HDrizzle/stack_machine/kicad/rendering_output/motherboard_render.png

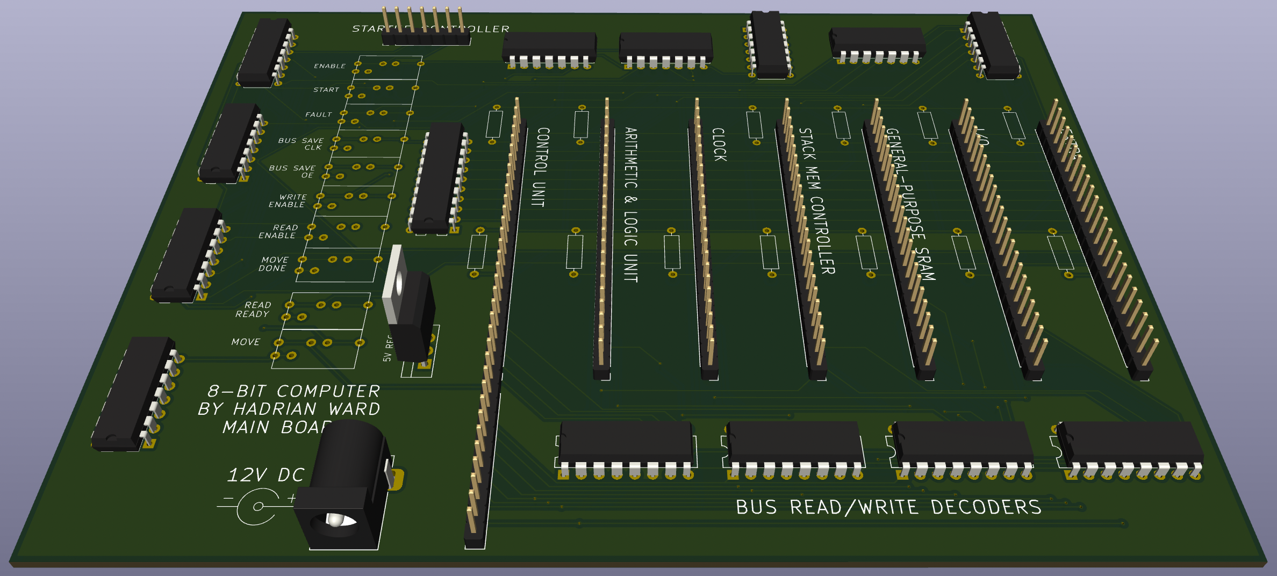
kicad/rendering_output/motherboard_render.png
