HDrizzle/stack_machine/presentation/images/actual_sequencer_cv.png

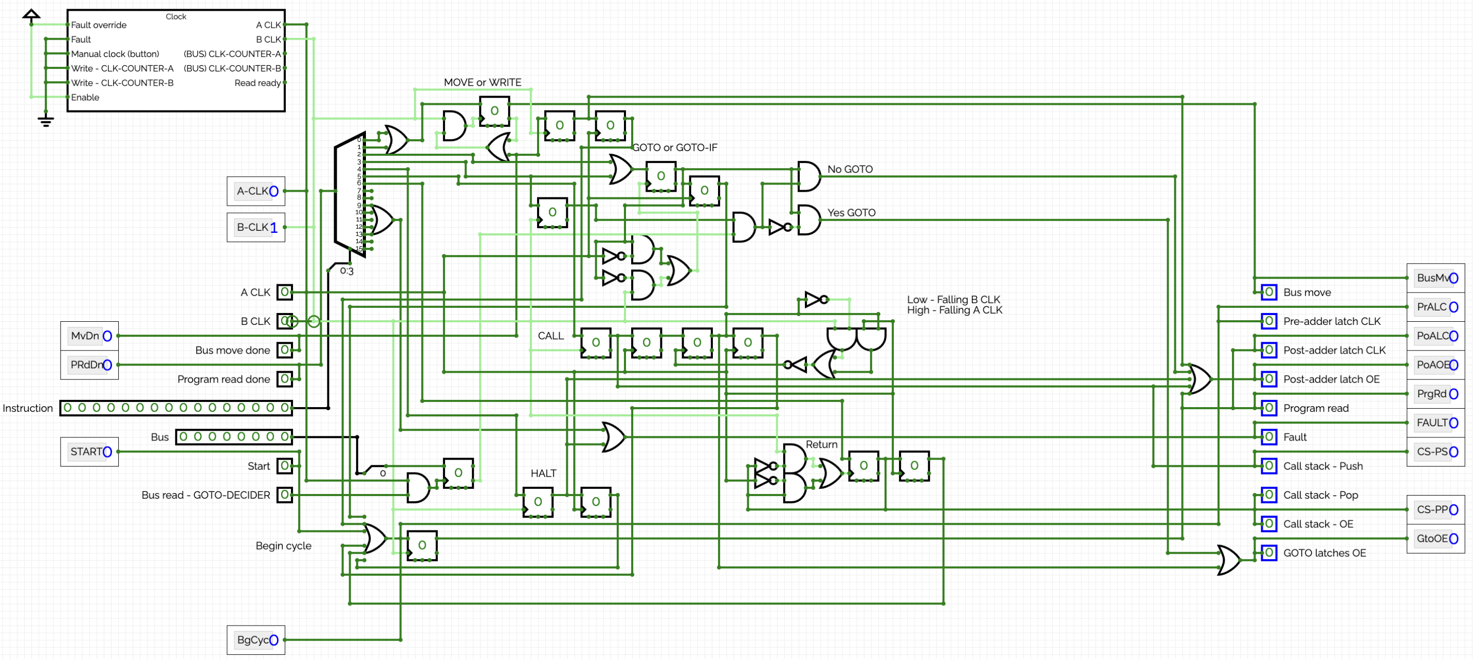
presentation/images/actual_sequencer_cv.png
