HDrizzle/stack_machine/presentation/images/bin_to_hex_gsheets.png

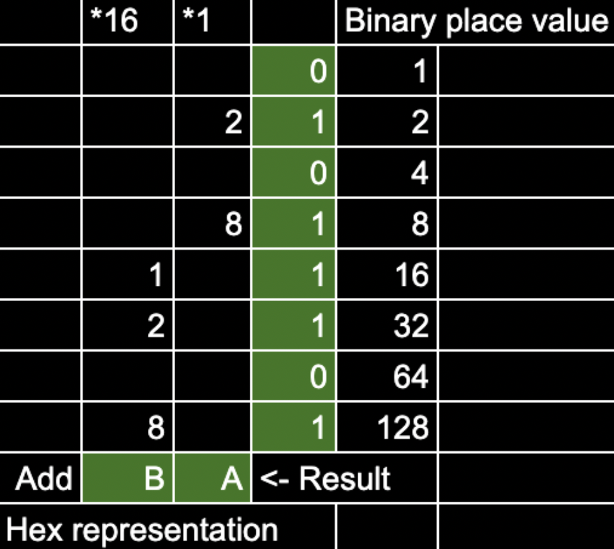
presentation/images/bin_to_hex_gsheets.png
