HDrizzle/stack_machine/presentation/images/bus_board.jpg

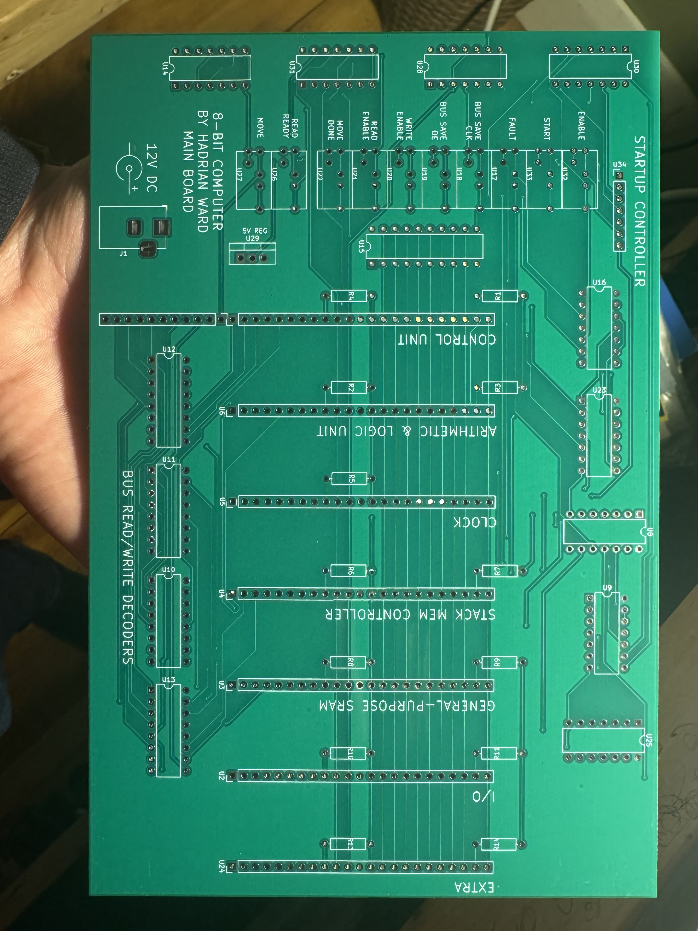
presentation/images/bus_board.jpg
