HDrizzle/stack_machine/presentation/images/bus_board_on_laptop.JPG

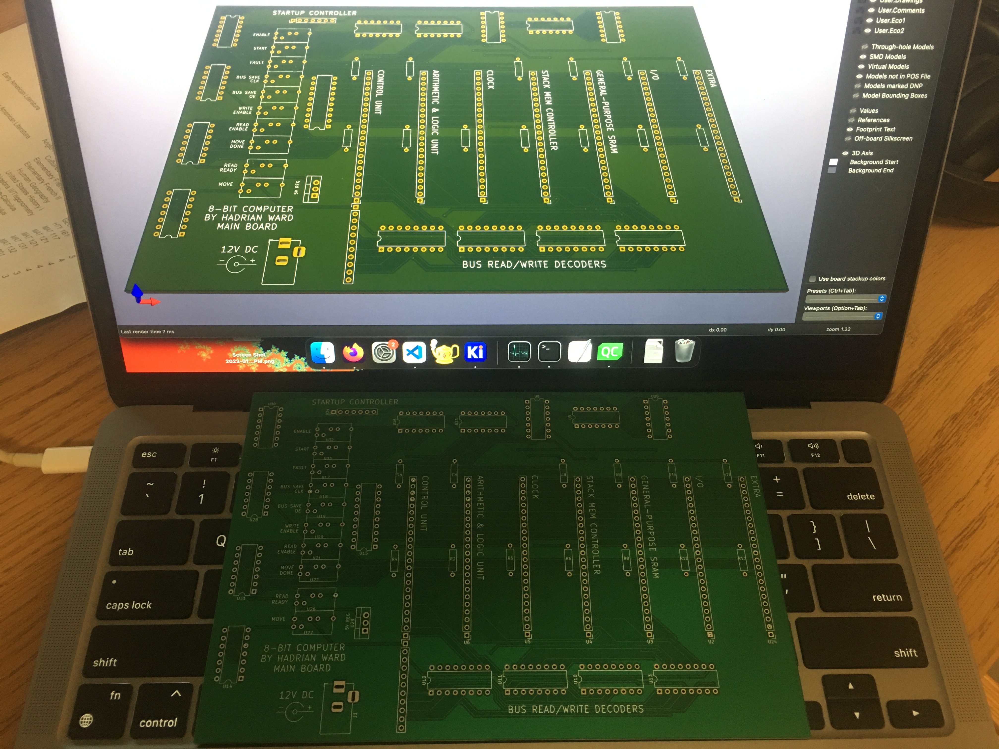
presentation/images/bus_board_on_laptop.JPG
