HDrizzle/stack_machine/presentation/images/chips.png

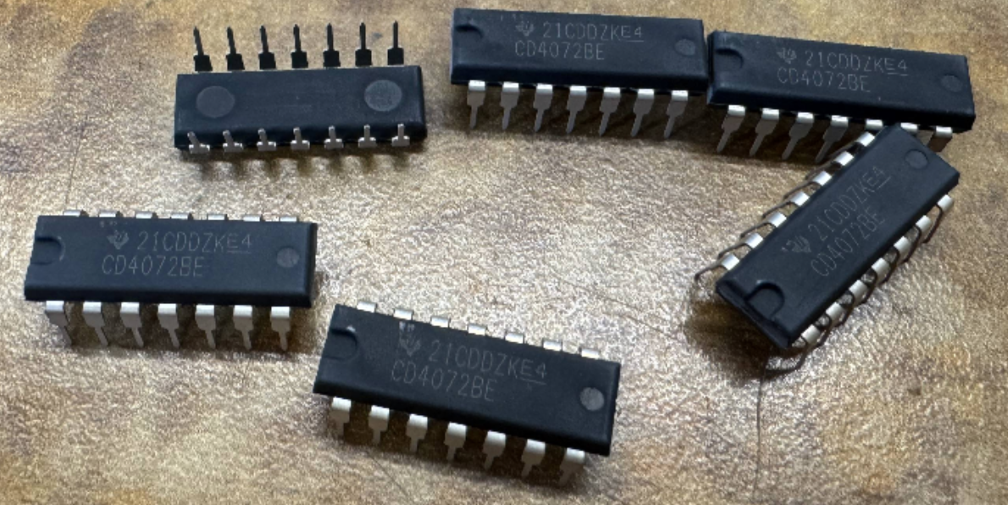
presentation/images/chips.png
