HDrizzle/stack_machine/presentation/images/complete_with_clock_on_scope.jpg

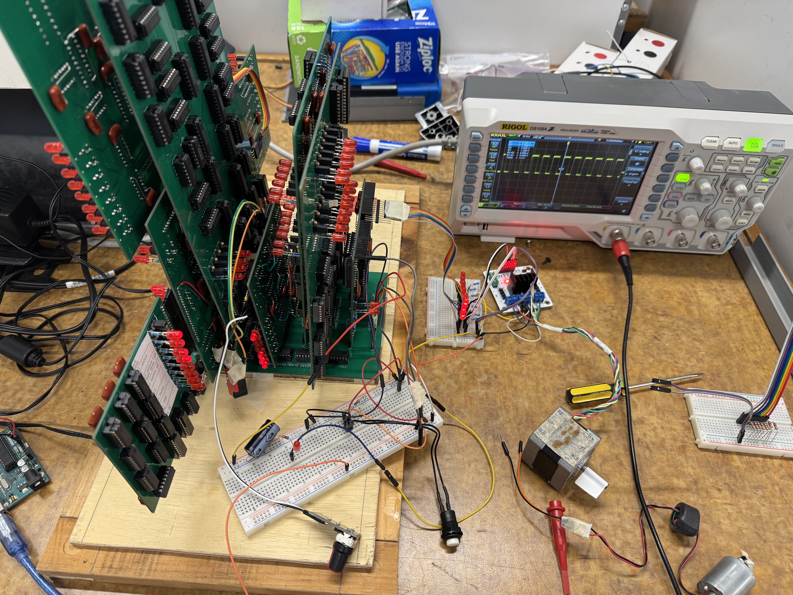
presentation/images/complete_with_clock_on_scope.jpg
