HDrizzle/stack_machine/presentation/images/cv_stack.png

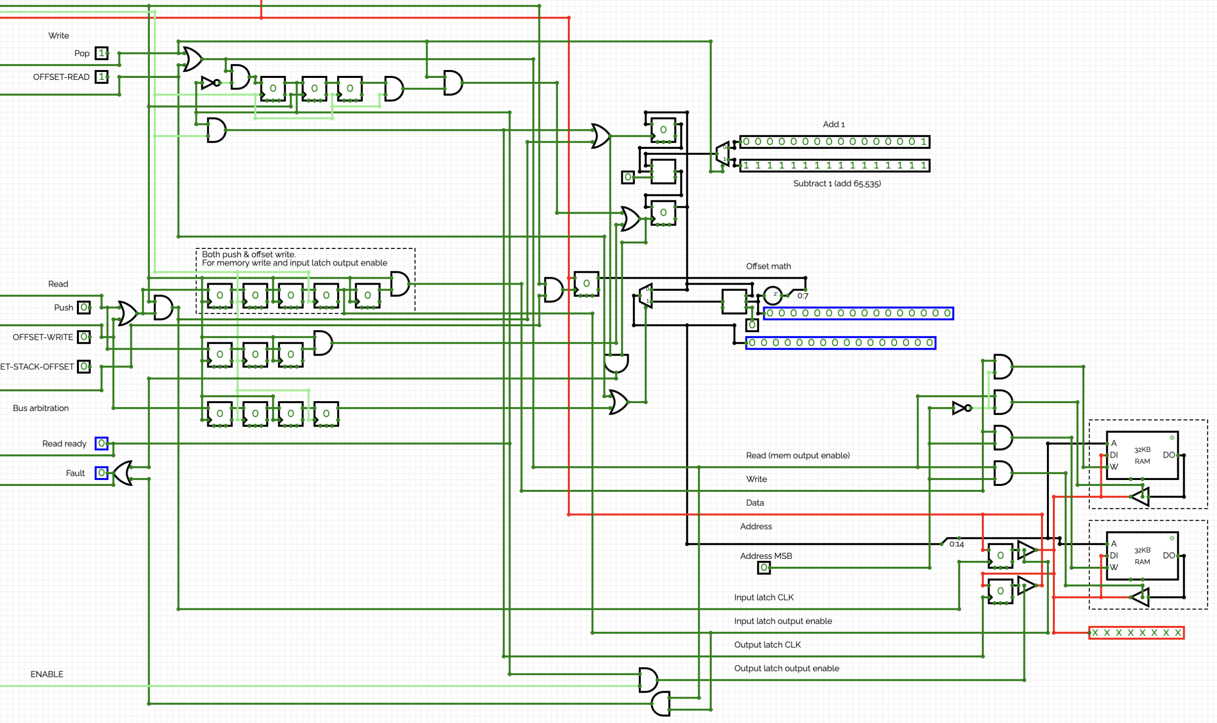
presentation/images/cv_stack.png
