HDrizzle/stack_machine/presentation/images/cv_timing_diagram.png

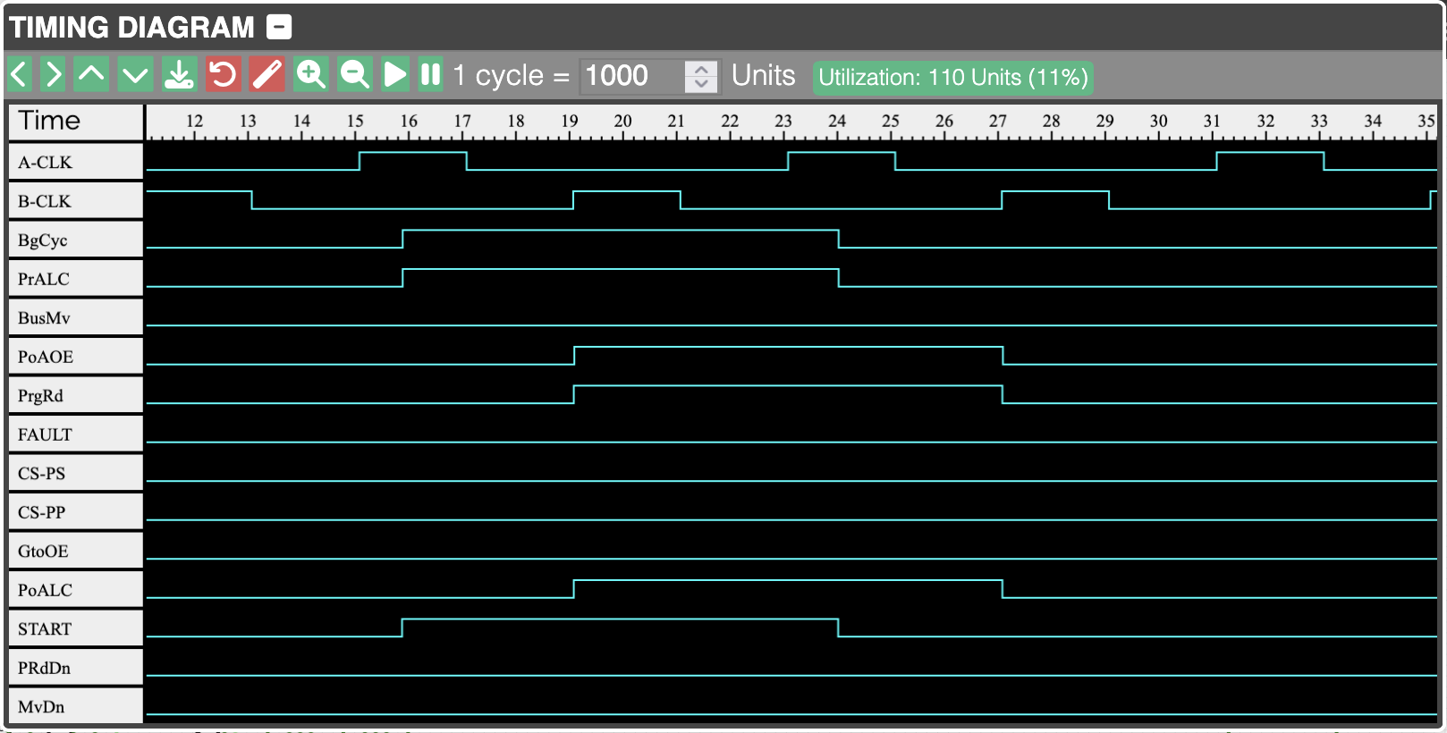
presentation/images/cv_timing_diagram.png
