HDrizzle/stack_machine/presentation/images/dram.png

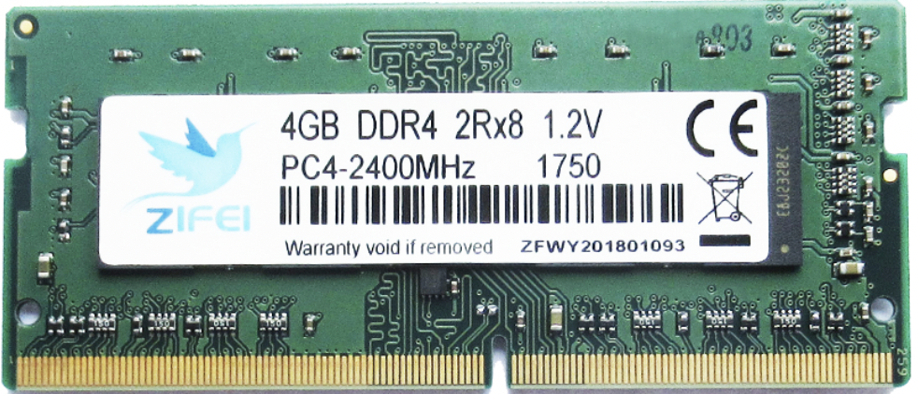
presentation/images/dram.png
