HDrizzle/stack_machine/presentation/images/flash.jpg

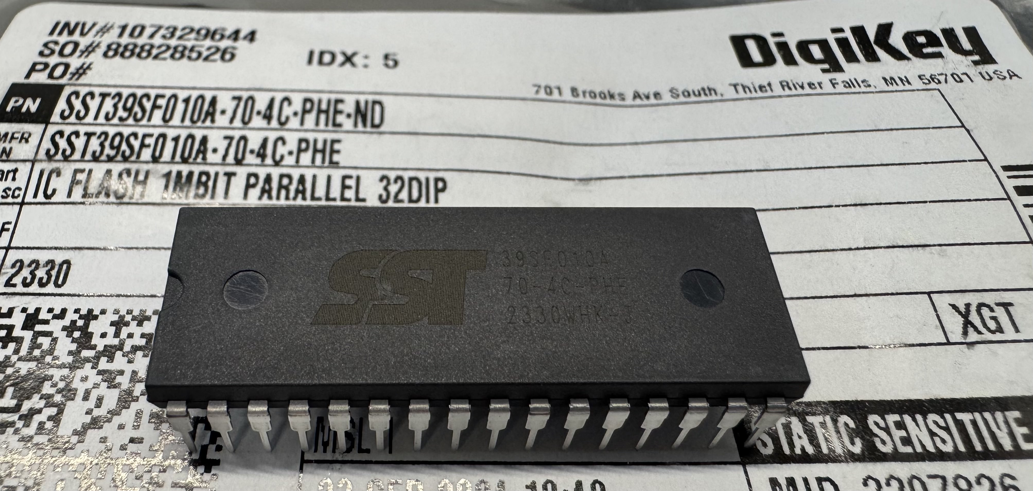
presentation/images/flash.jpg
