HDrizzle/stack_machine/presentation/images/gpram.jpg

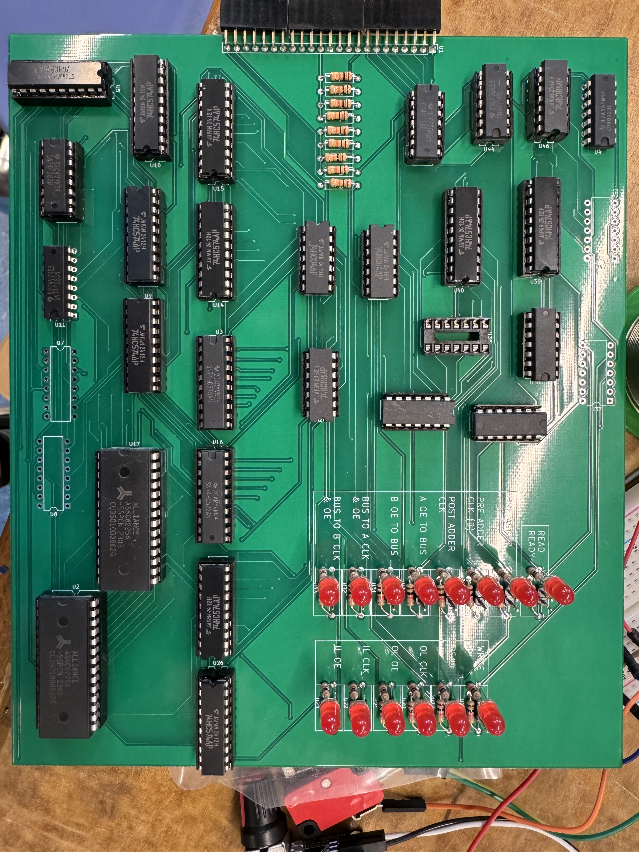
presentation/images/gpram.jpg
