HDrizzle/stack_machine/presentation/images/gpu.jpg

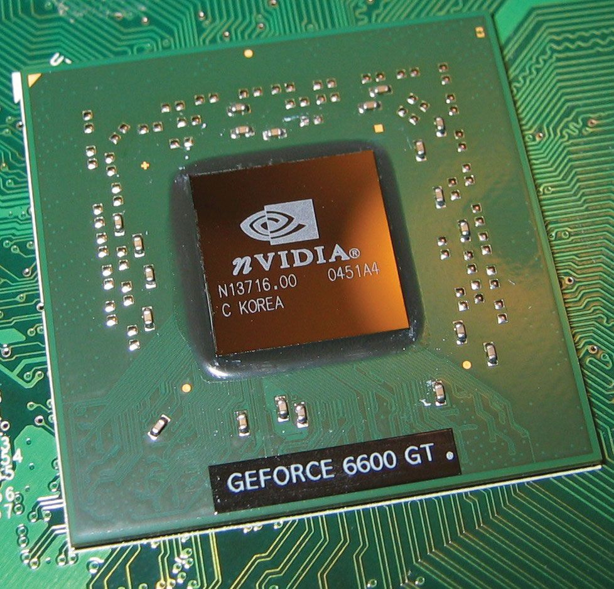
presentation/images/gpu.jpg
