HDrizzle/stack_machine/presentation/images/kicad_bus_pcb_scrot.png

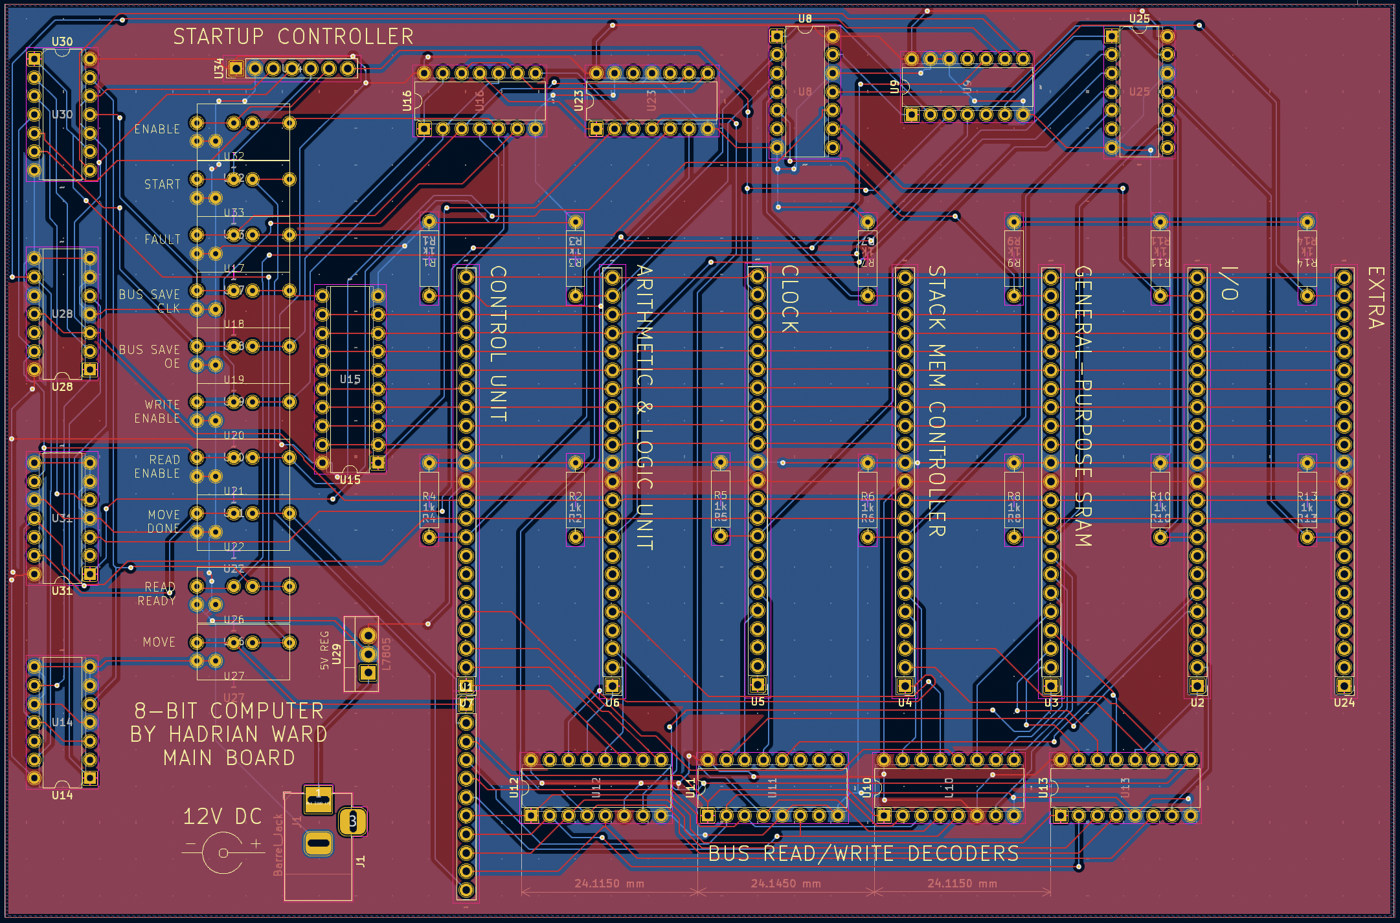
presentation/images/kicad_bus_pcb_scrot.png
