HDrizzle/stack_machine/presentation/images/led_off.jpeg

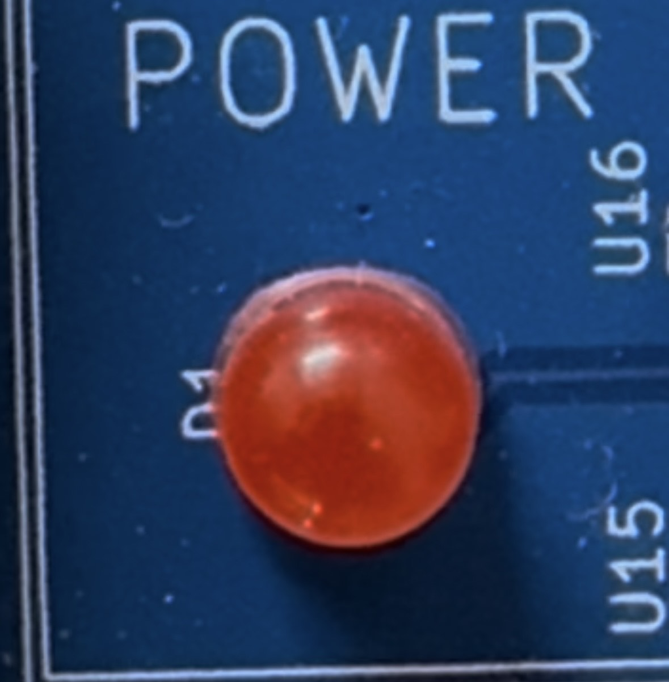
presentation/images/led_off.jpeg
