HDrizzle/stack_machine/presentation/images/led_on.jpeg

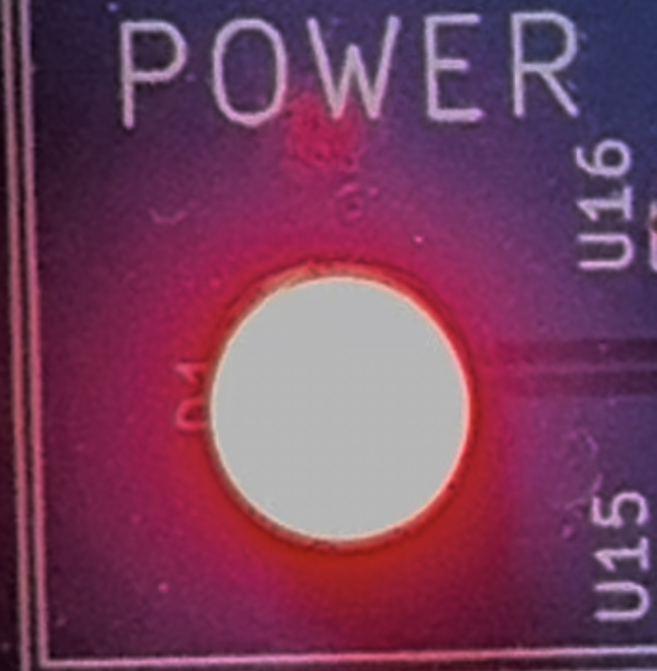
presentation/images/led_on.jpeg
