HDrizzle/stack_machine/presentation/images/led_tiles_in_place.jpg

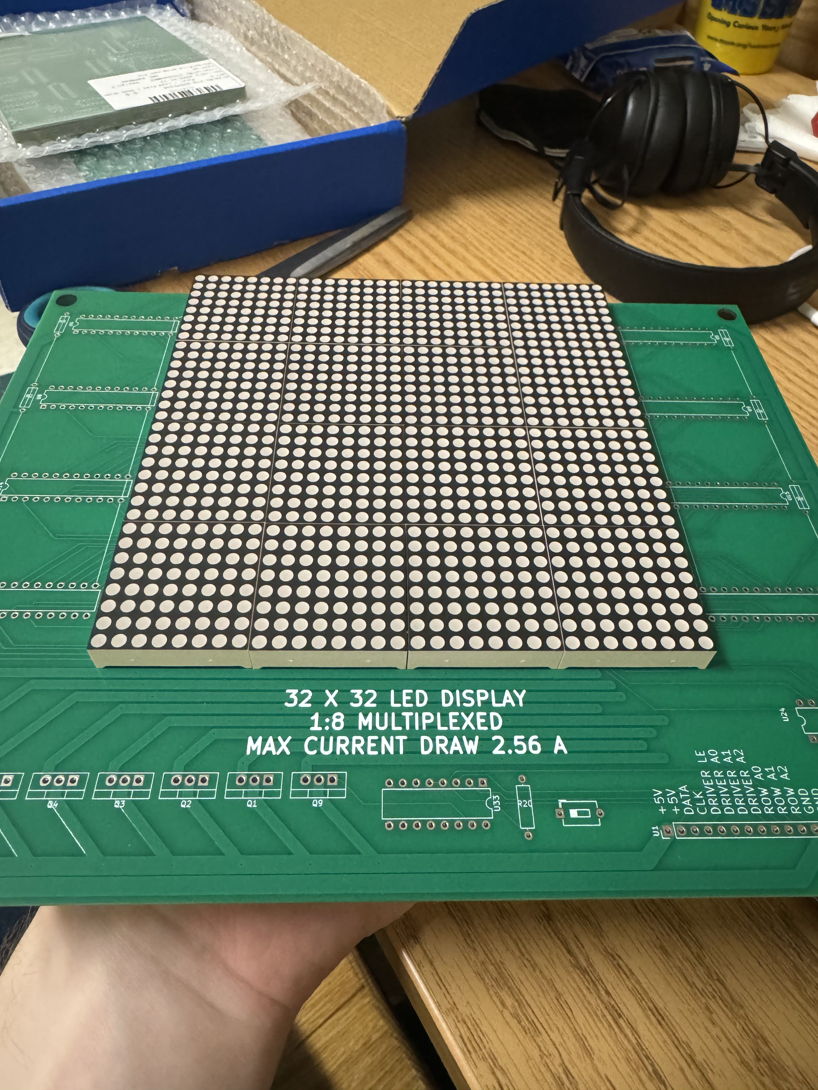
presentation/images/led_tiles_in_place.jpg
