HDrizzle/stack_machine/presentation/images/main_block_diagram.png

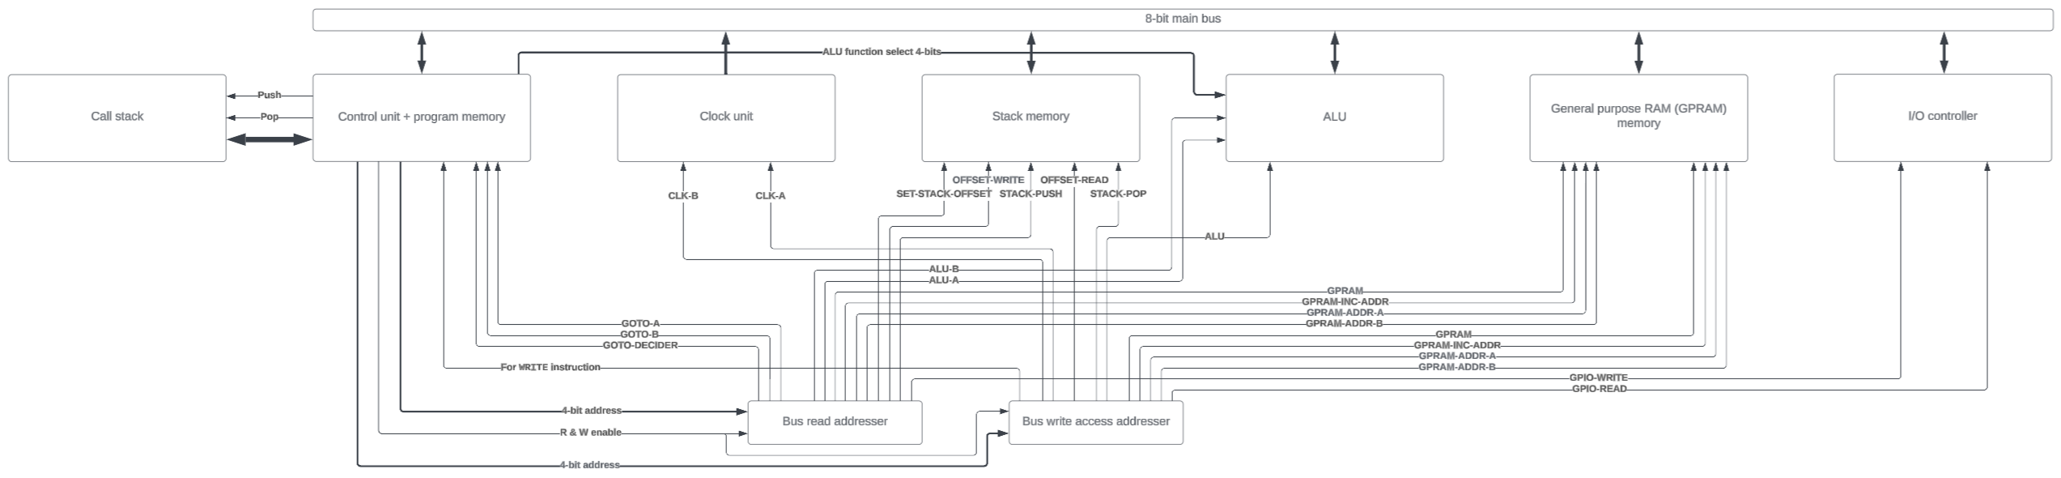
presentation/images/main_block_diagram.png
