HDrizzle/stack_machine/presentation/images/nice_signal_on_scope.jpg

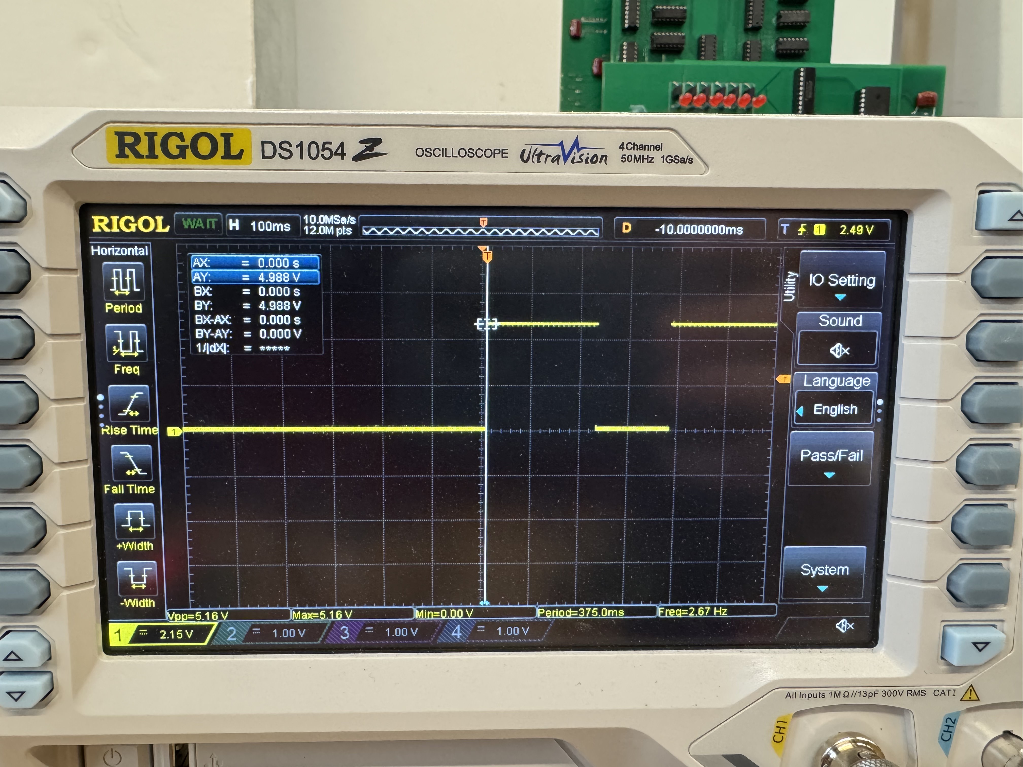
presentation/images/nice_signal_on_scope.jpg
