HDrizzle/stack_machine/presentation/images/partially_completed_powered.jpg

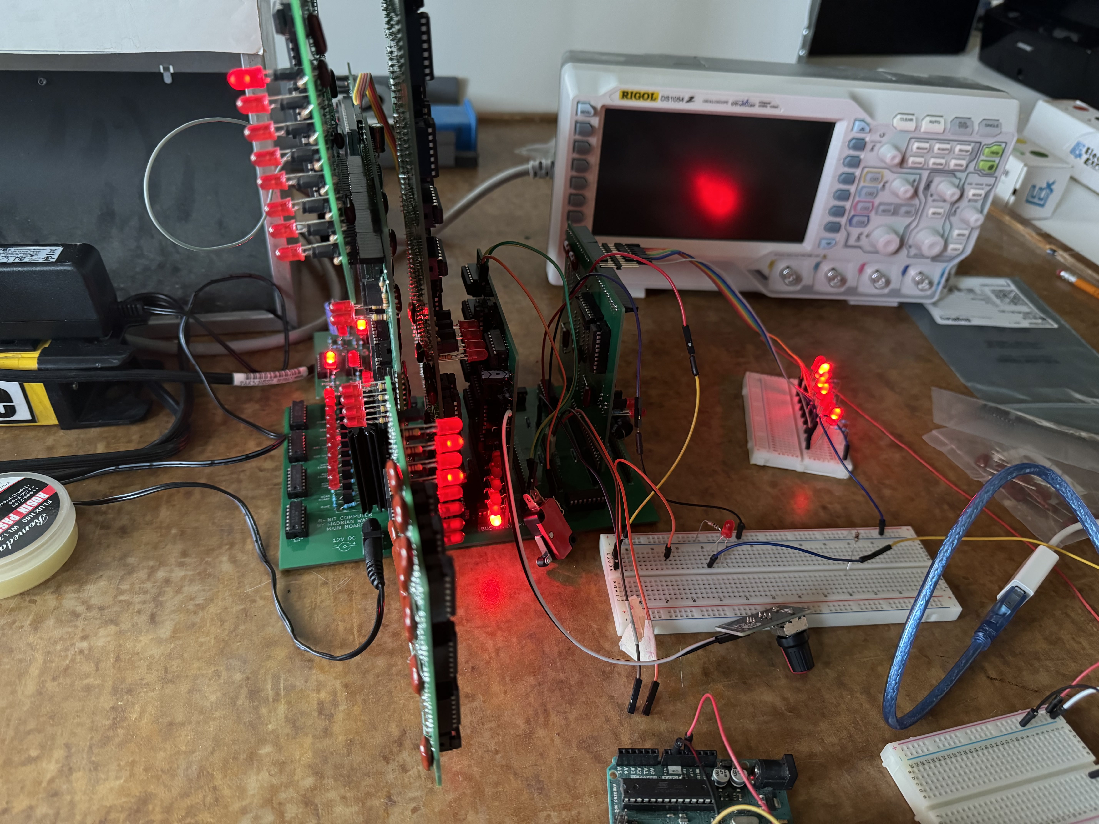
presentation/images/partially_completed_powered.jpg
