HDrizzle/stack_machine/presentation/images/photo_8_bit_latch.jpeg

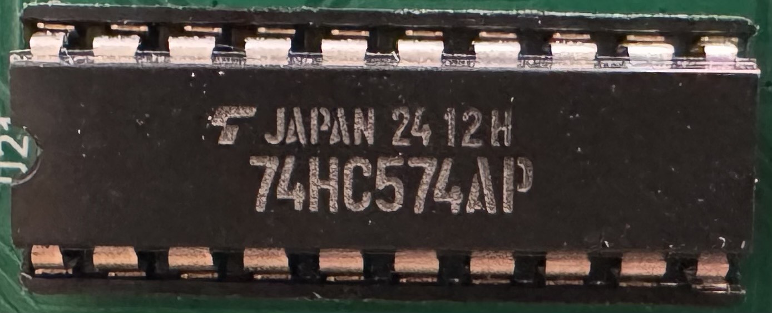
presentation/images/photo_8_bit_latch.jpeg
