HDrizzle/stack_machine/presentation/images/photo_bus_timing.jpeg

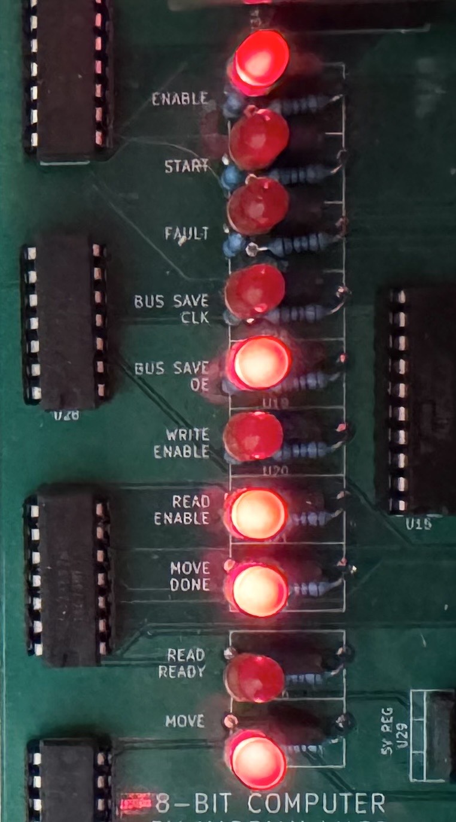
presentation/images/photo_bus_timing.jpeg
