HDrizzle/stack_machine/presentation/images/photo_call_stack.jpeg

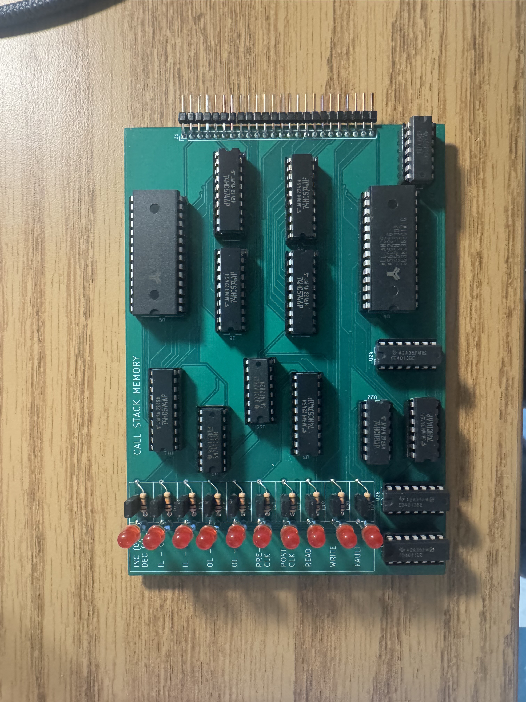
presentation/images/photo_call_stack.jpeg
