HDrizzle/stack_machine/presentation/images/photo_central_timing.jpeg

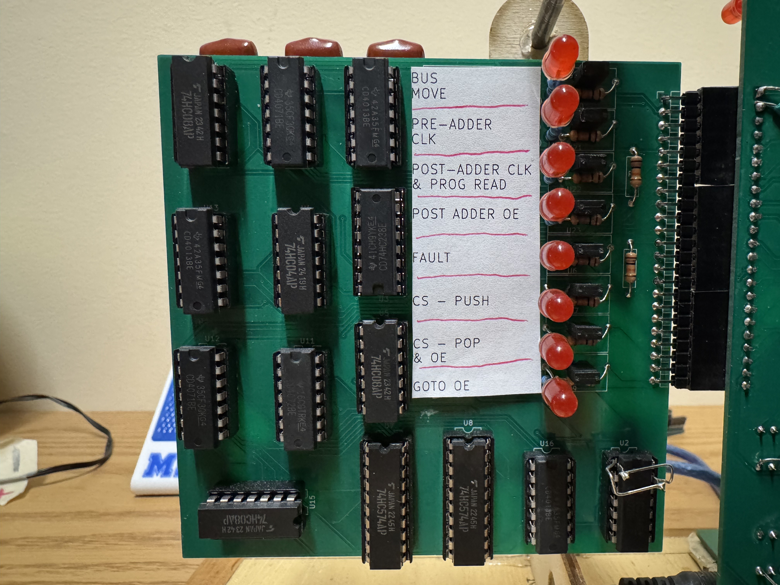
presentation/images/photo_central_timing.jpeg
