HDrizzle/stack_machine/presentation/images/photo_prog_mem.jpeg

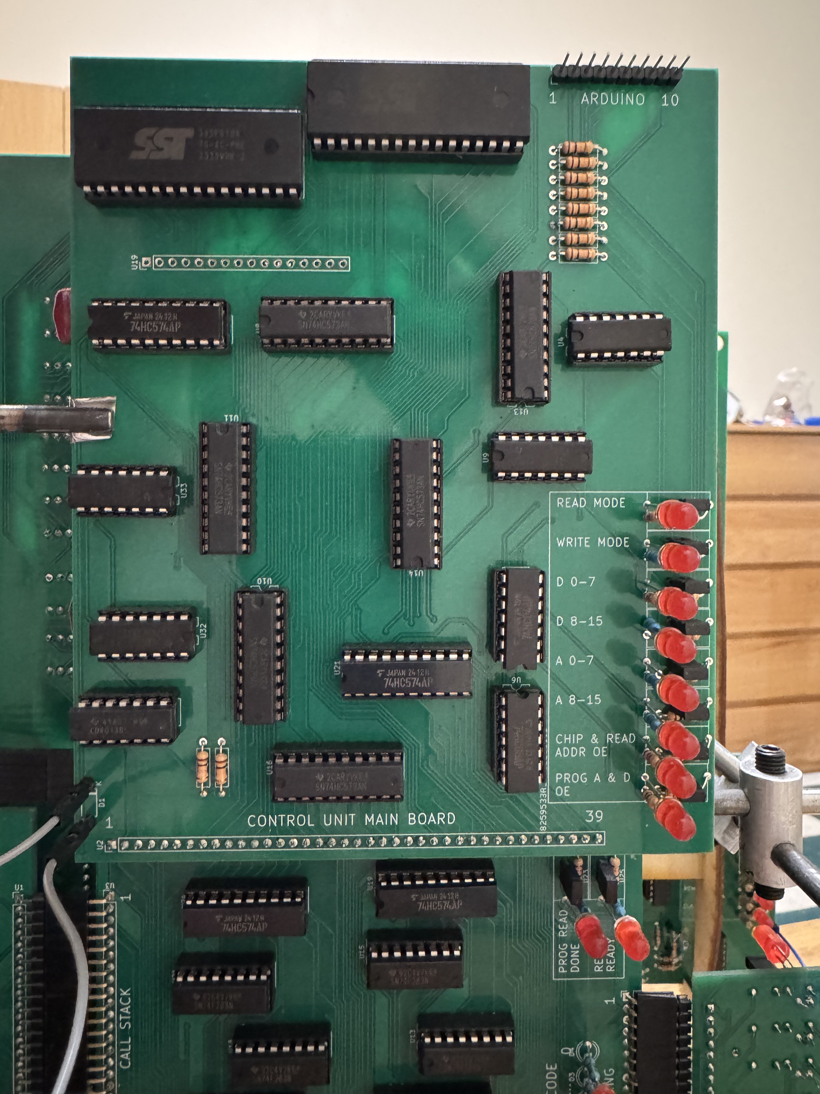
presentation/images/photo_prog_mem.jpeg
