HDrizzle/stack_machine/presentation/images/photo_quad_and.jpeg

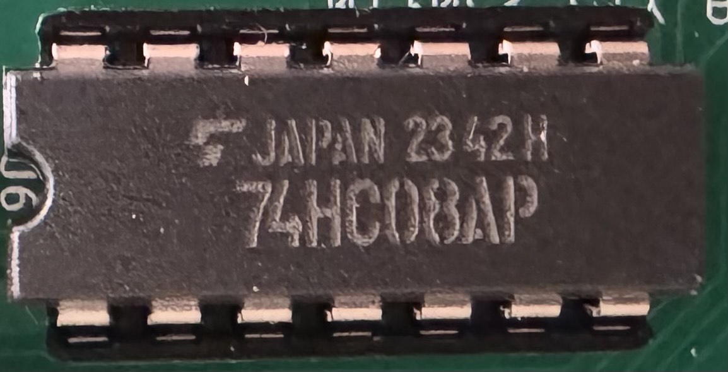
presentation/images/photo_quad_and.jpeg
