HDrizzle/stack_machine/presentation/images/photo_starter.jpeg

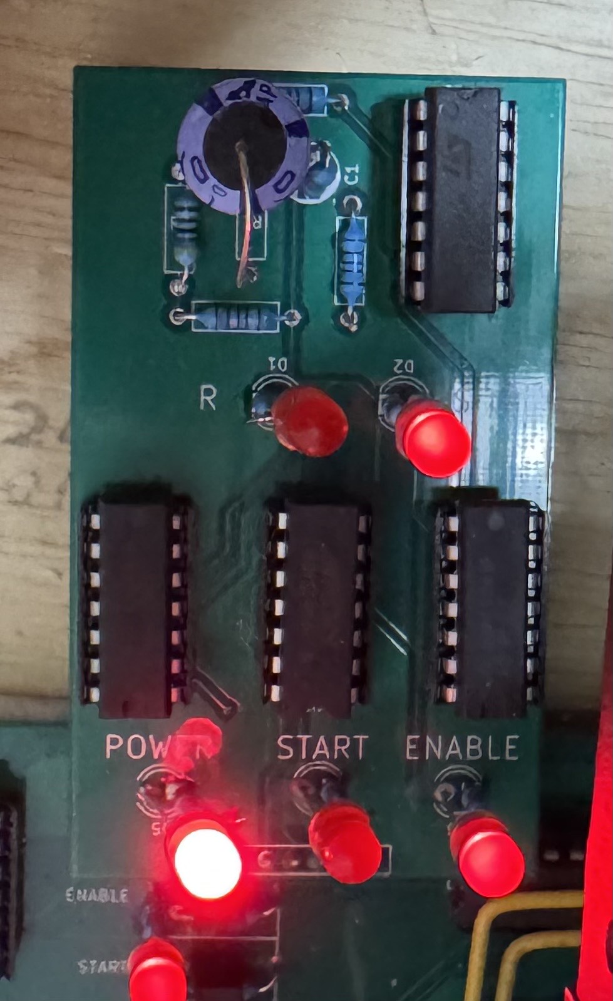
presentation/images/photo_starter.jpeg
