HDrizzle/stack_machine/presentation/images/scrot_bus_dests.png

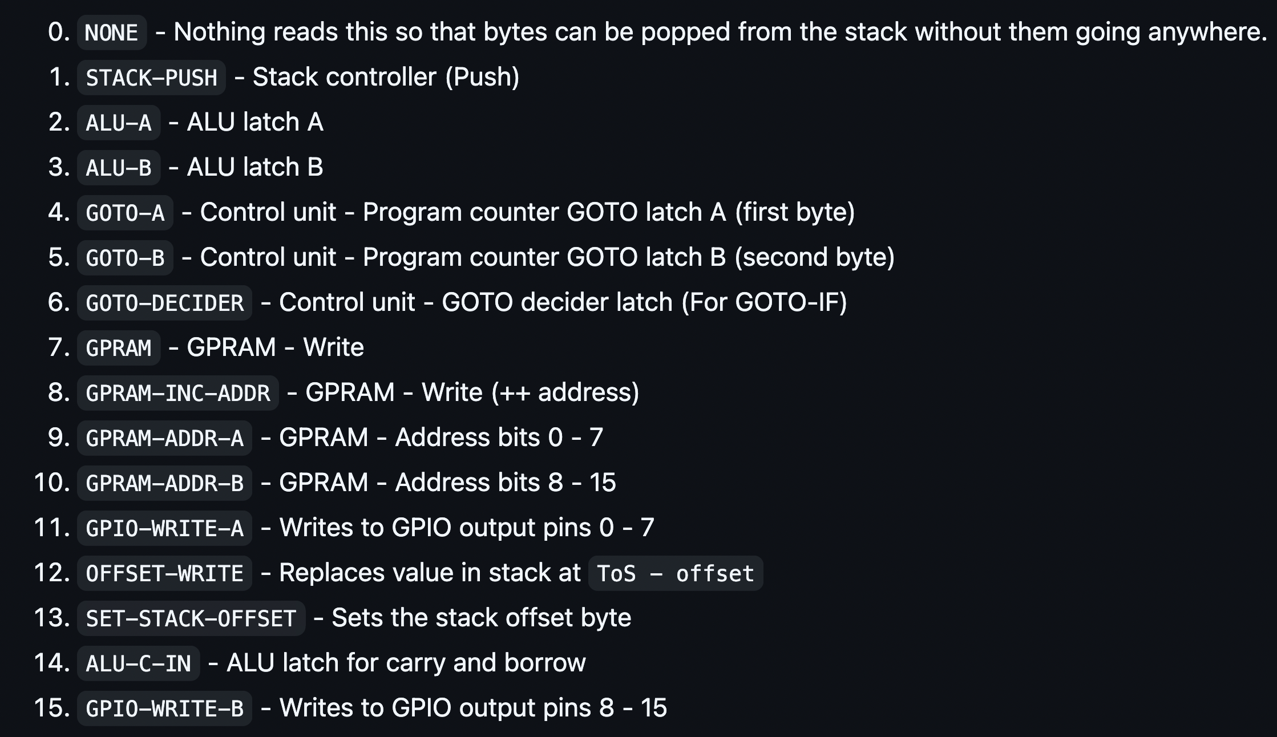
presentation/images/scrot_bus_dests.png
