HDrizzle/stack_machine/presentation/images/scrot_bus_sources.png

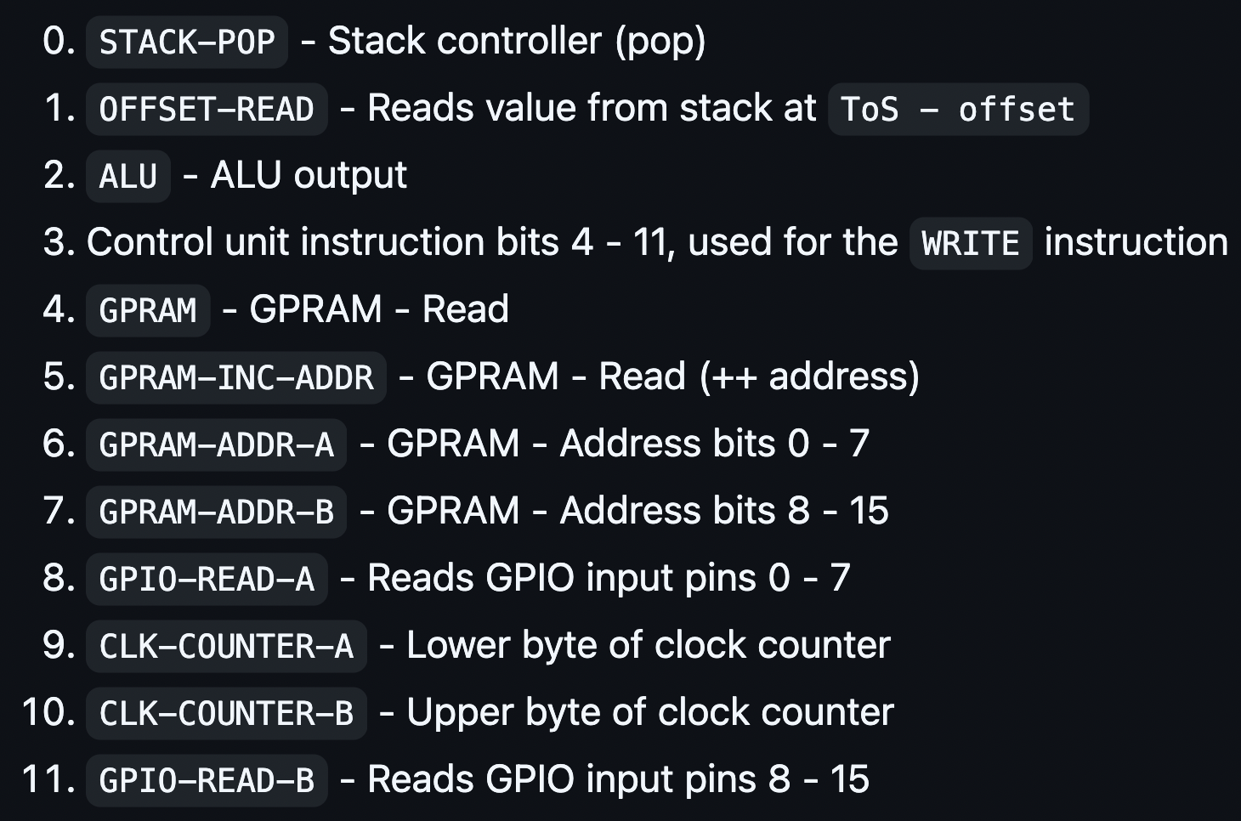
presentation/images/scrot_bus_sources.png
