HDrizzle/stack_machine/presentation/images/signal_interference.JPG

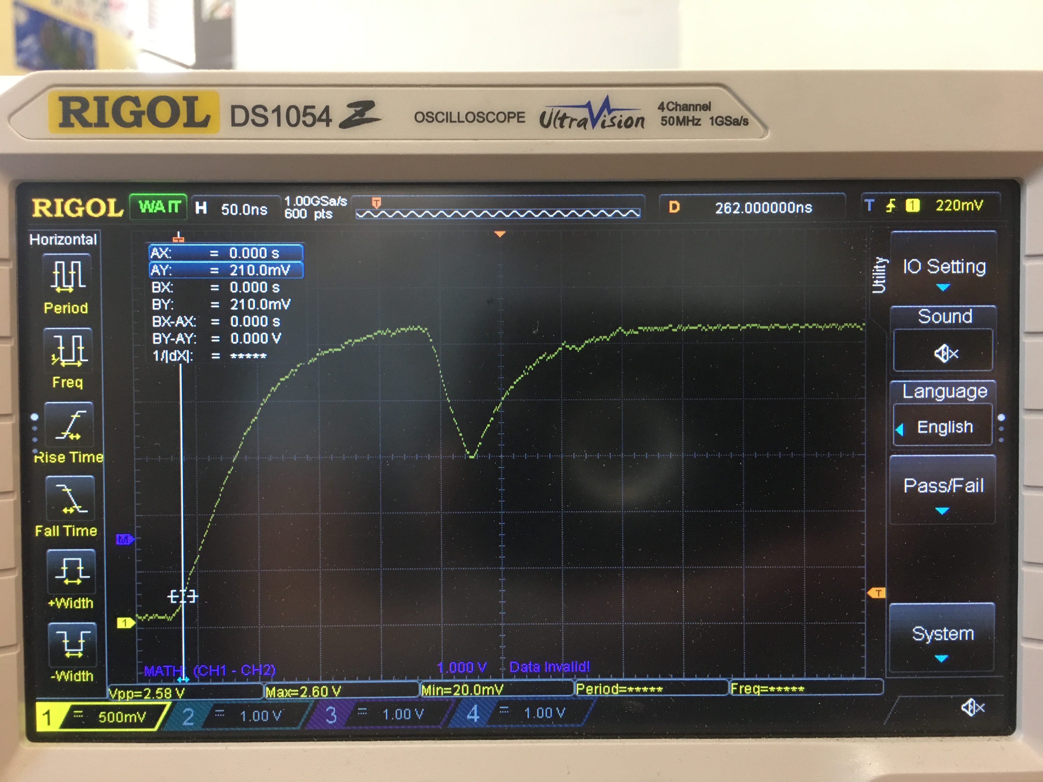
presentation/images/signal_interference.JPG
