HDrizzle/stack_machine/presentation/images/sram.jpg

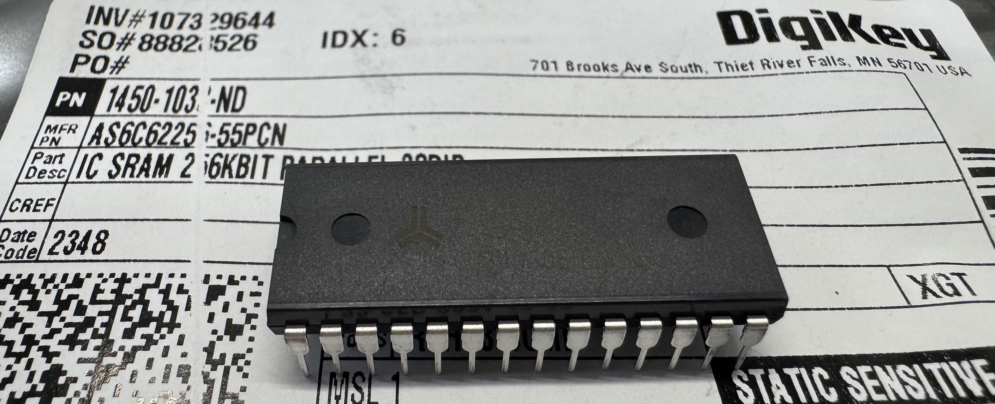
presentation/images/sram.jpg
