HDrizzle/stack_machine/presentation/images/sram_top_down.jpeg

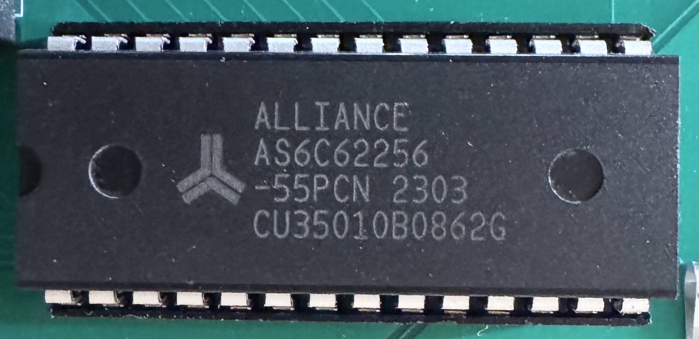
presentation/images/sram_top_down.jpeg
