HDrizzle/stack_machine/presentation/images/title_slide_background.png

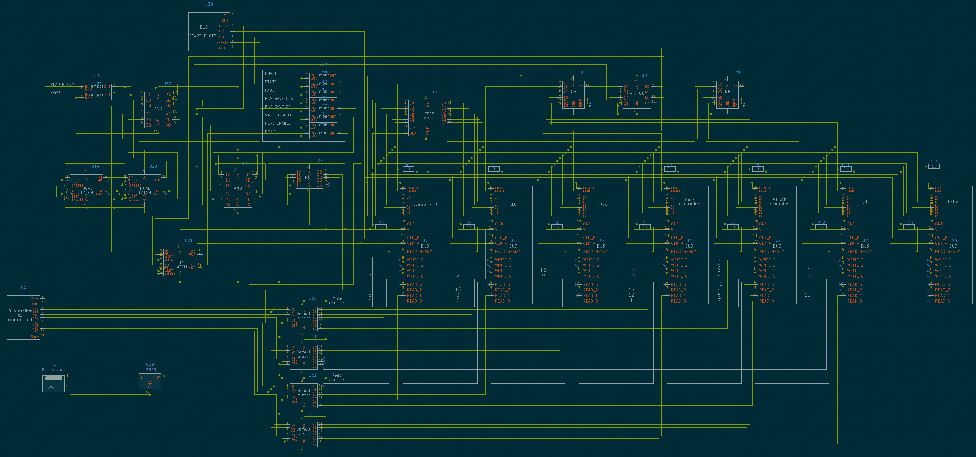
presentation/images/title_slide_background.png
