HDrizzle/stack_machine/presentation/images/view_with_alu_missing.jpg

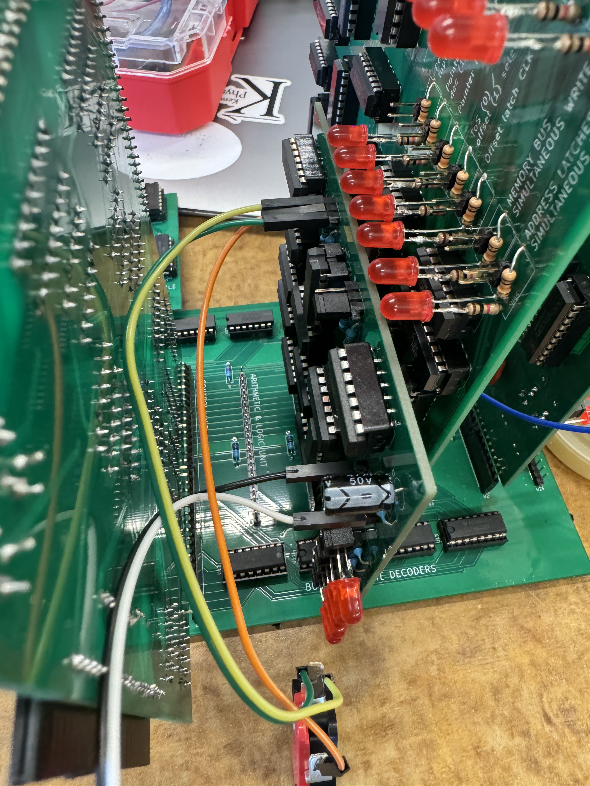
presentation/images/view_with_alu_missing.jpg
