HDrizzle/stack_machine/presentation/images/wavedrom_main_cycle.png

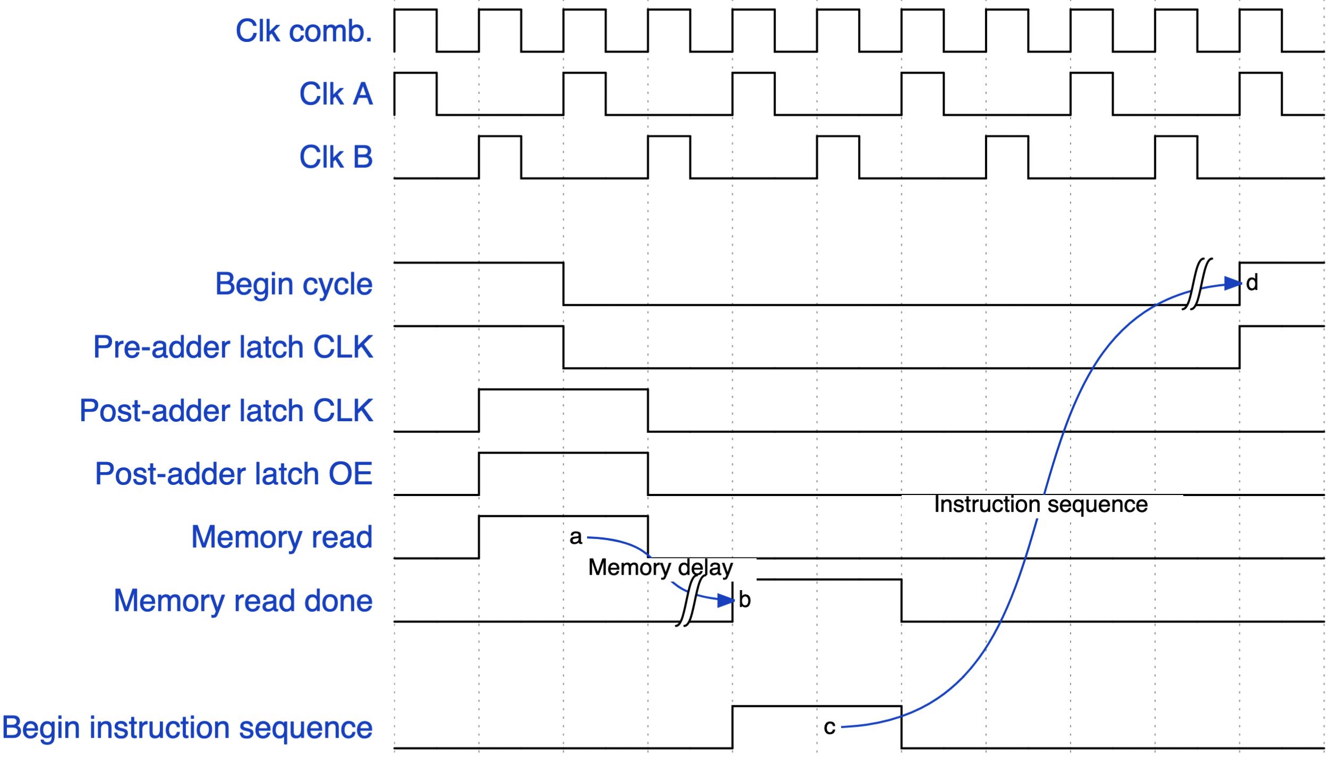
presentation/images/wavedrom_main_cycle.png
