HDrizzle/stack_machine/kicad/boards_version_2/stack_data_v2/stack_data_v2.kicad_pcb

## KiCad design schematics/schematics.kicad_sch

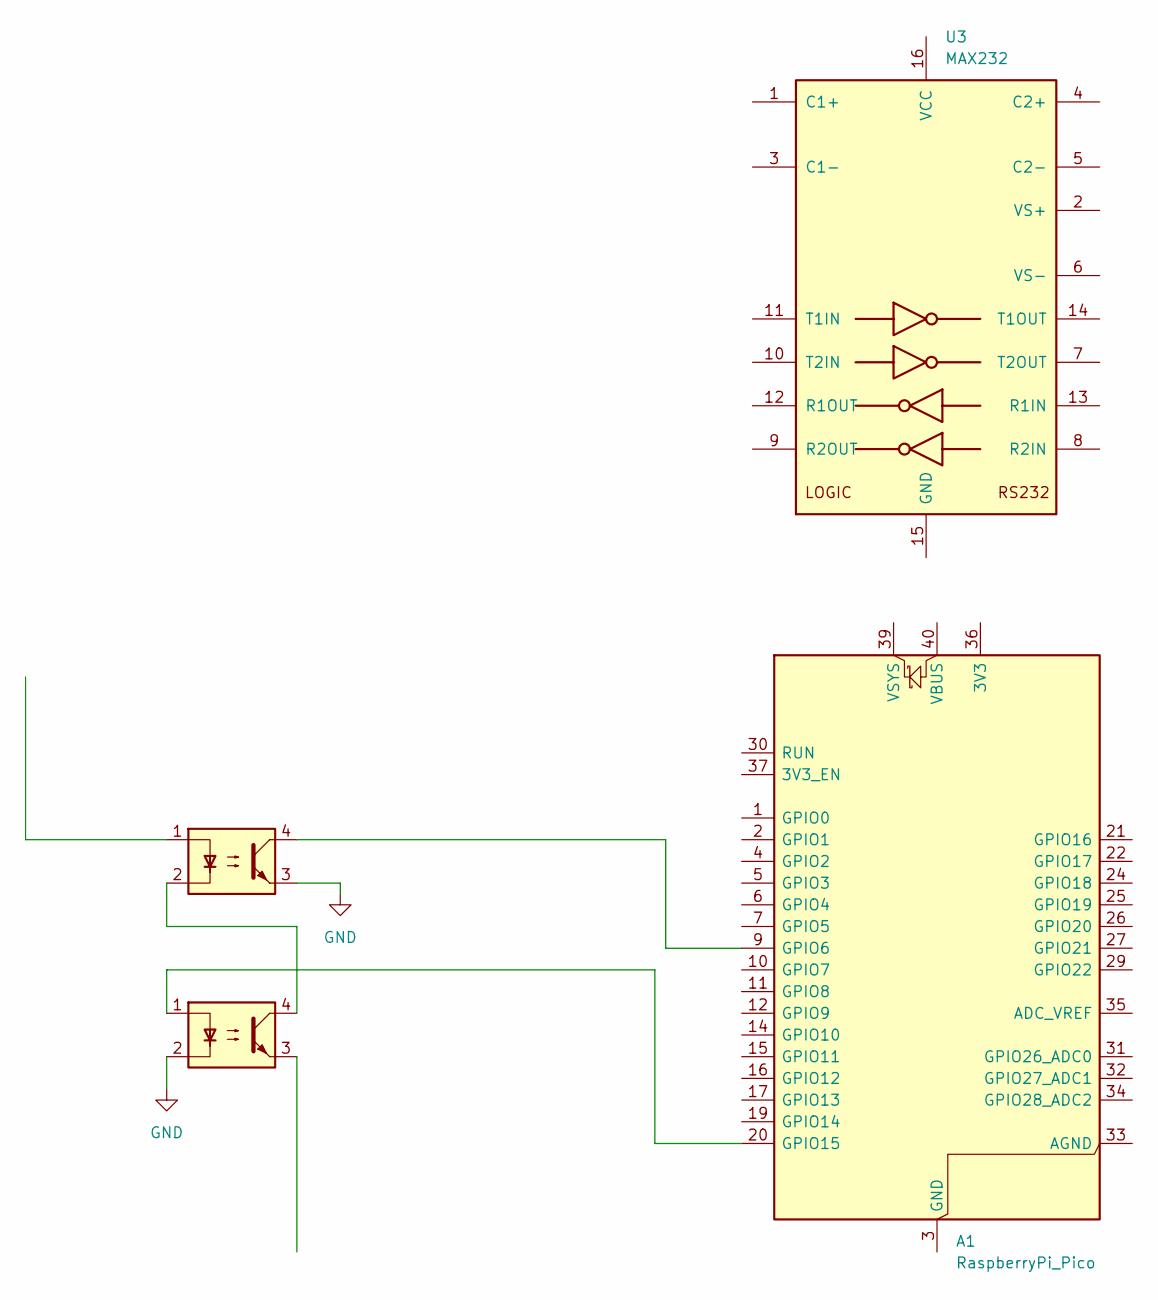
[picture p47: schematic schematics.kicad_sch]

Parts:
A1: RaspberryPi_Pico; RaspberryPi_Pico_Common_Unspecified
U1, U2: SFH617A-1X001; DIP-4_W7.62mm
U3: MAX232

Connections:
GND: U1.3, U2.2
unnamed: A1.9 (GPIO6), U1.4
unnamed: A1.3 (GND), A1.8 (GND), A1.13 (GND), A1.18 (GND), A1.23 (GND), A1.28 (GND), A1.38 (GND)
unnamed: A1.20 (GPIO15), U2.1
unnamed: U1.2, U2.4
