HDrizzle/stack_machine/presentation/images/clock_with_switches_connected.jpg

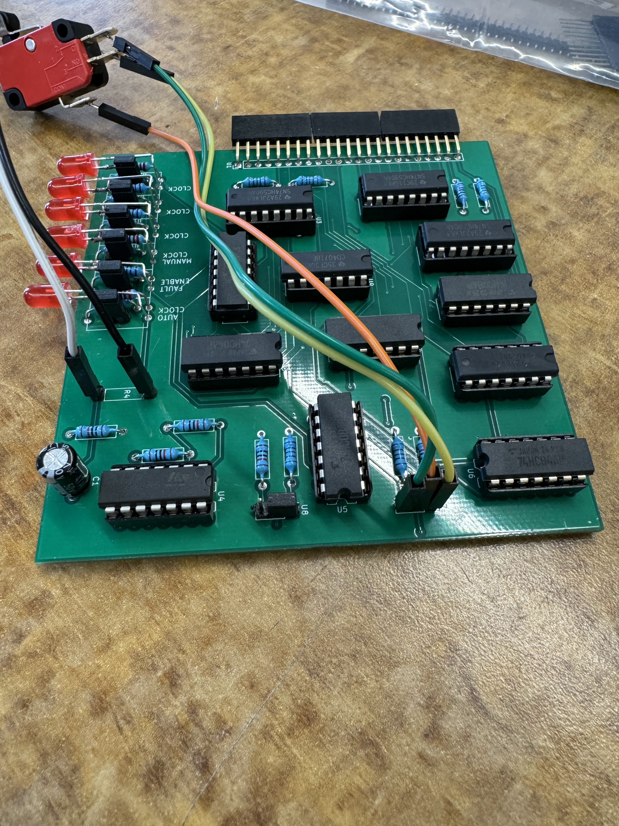
presentation/images/clock_with_switches_connected.jpg
