HDrizzle/stack_machine/presentation/images/display_controller_partial_hookup.jpg

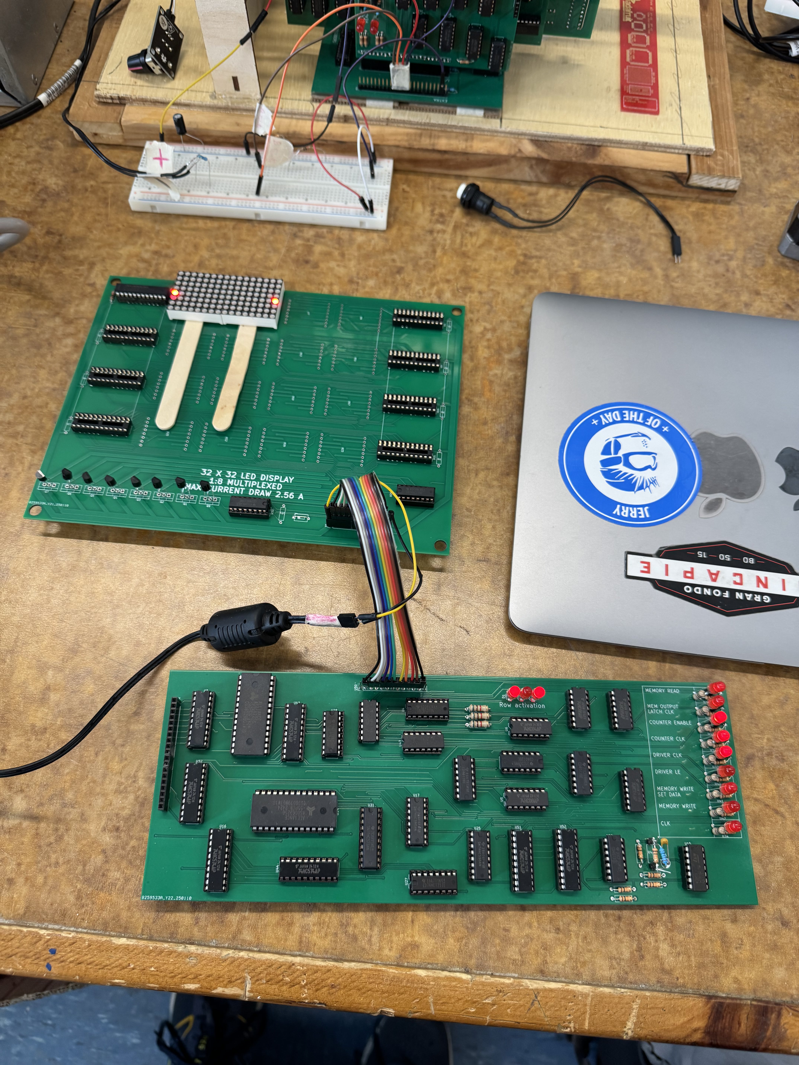
presentation/images/display_controller_partial_hookup.jpg
