HDrizzle/stack_machine/presentation/images/etching.jpeg

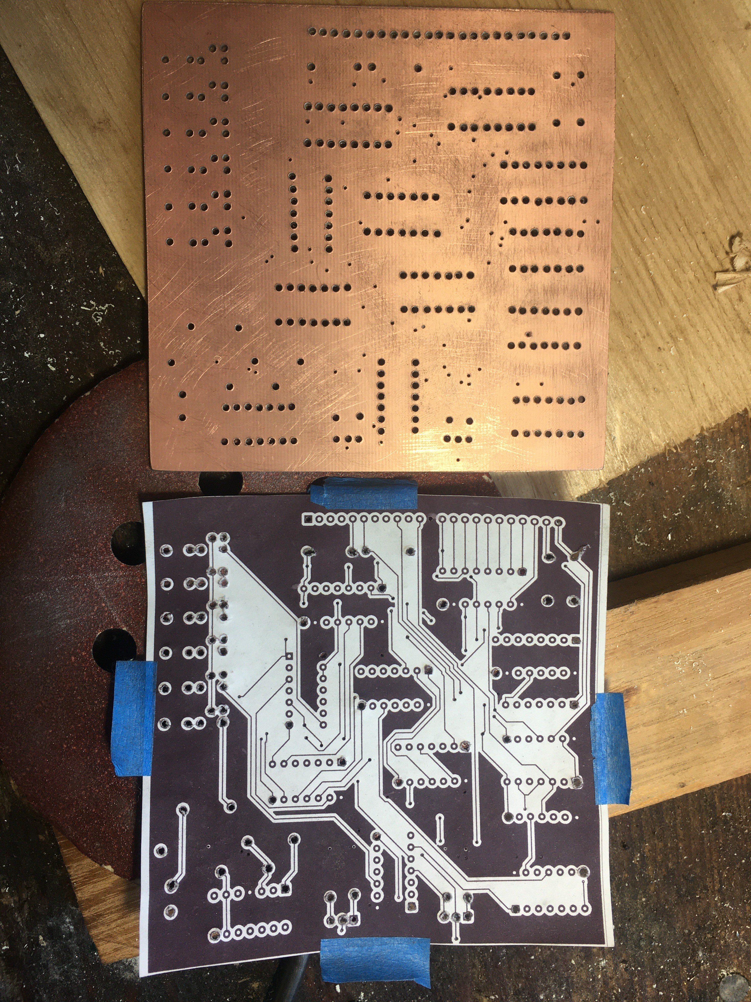
presentation/images/etching.jpeg
