HDrizzle/stack_machine/presentation/images/first_structural_supports.jpg

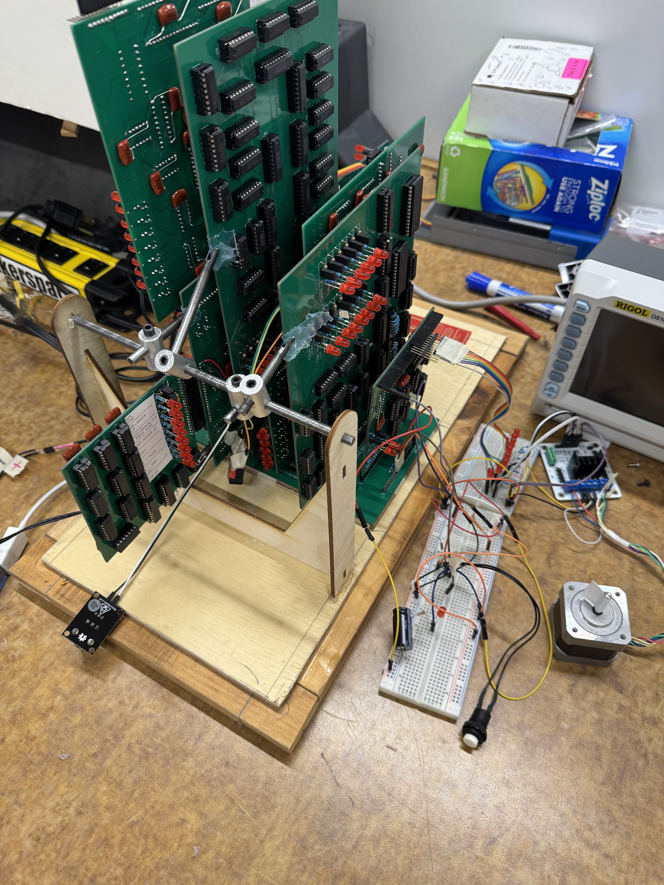
presentation/images/first_structural_supports.jpg
